uvknhn/quad-creek/docs/img/106.jpg

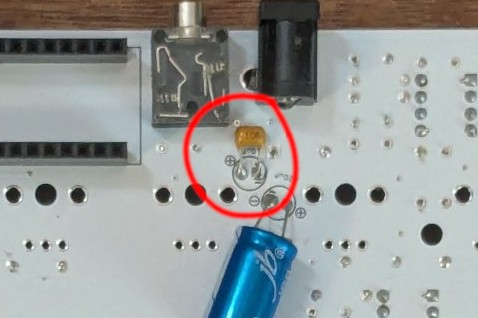
docs/img/106.jpg
