uvknhn/quad-creek/docs/img/PCB_Step_1.jpg

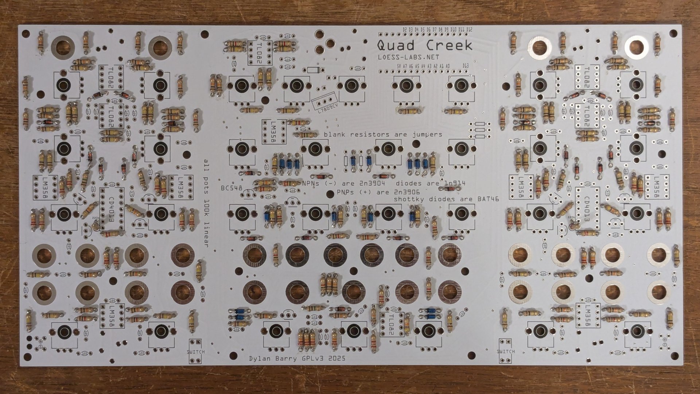
docs/img/PCB_Step_1.jpg
