uvknhn/quad-creek/docs/img/PCB_Step_2.jpg

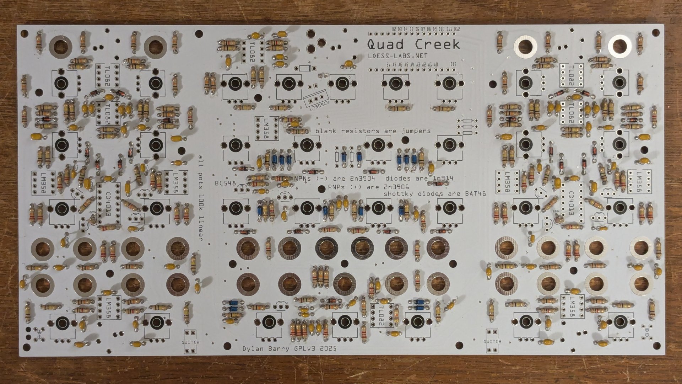
docs/img/PCB_Step_2.jpg
