uvknhn/quad-creek/docs/img/PCB_Step_5.jpg

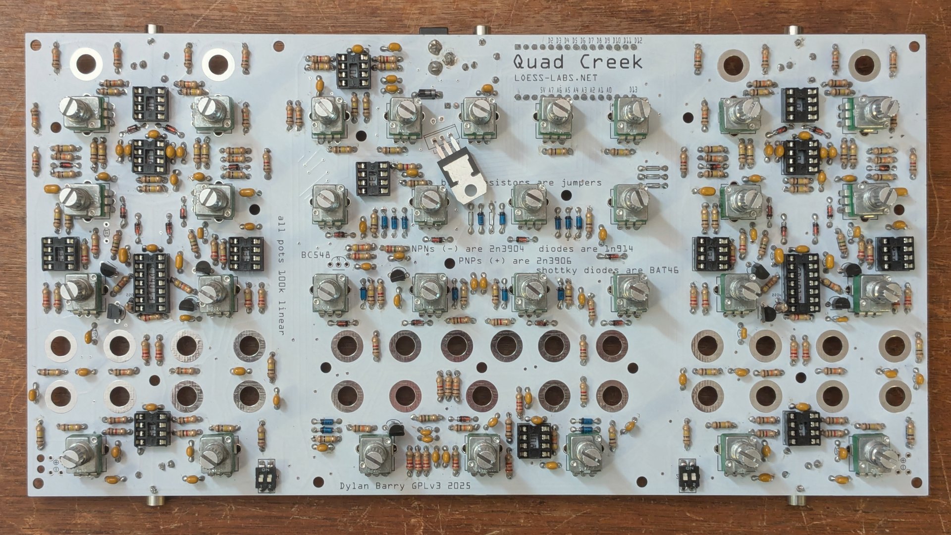
docs/img/PCB_Step_5.jpg
