uvknhn/quad-creek/docs/img/PCB_Step_6.jpg

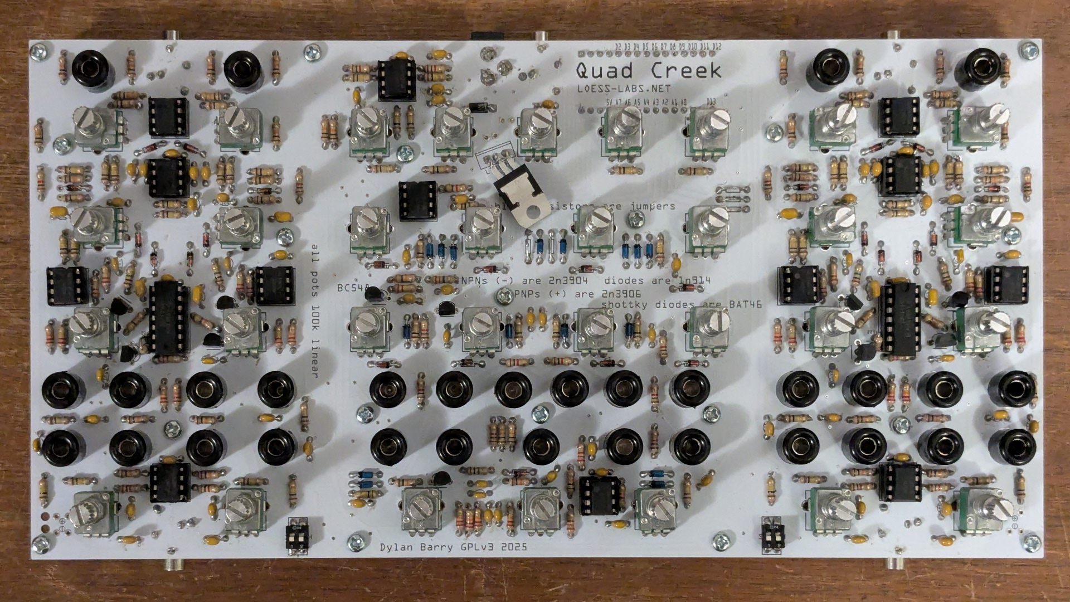
docs/img/PCB_Step_6.jpg
